Props3D/se14r-blaster/models/SE-14r_ScopeMount_V4.stl

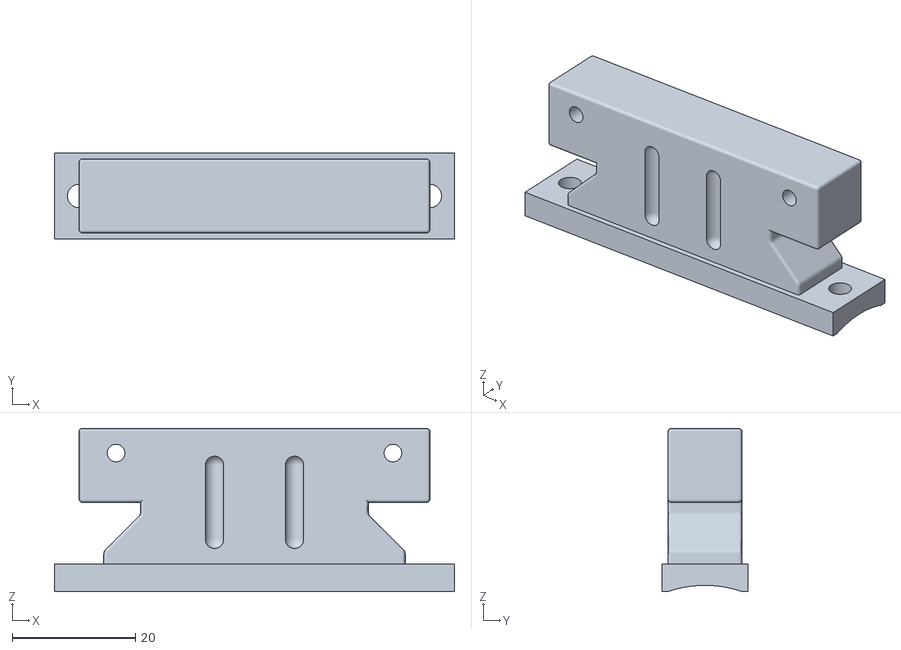
[picture p15: CAD file, 2021-10-15]
models/SE-14r_ScopeMount_V4.stl
65.0 x 14.0 x 26.5
