Props3D/se14r-blaster/models/SE-14r_UpperBack_V4.stl

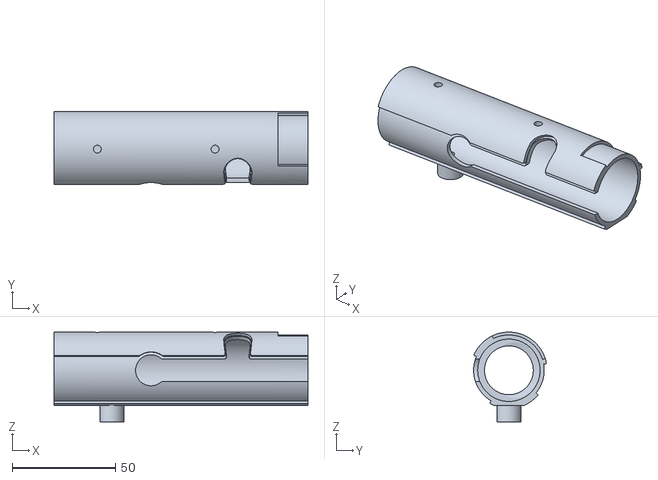
[picture p16: CAD file, 2021-10-15]
models/SE-14r_UpperBack_V4.stl
123.0 x 35.3 x 43.5
