Props3D/se14r-blaster/models/SE-14r_UpperFront_V4.stl

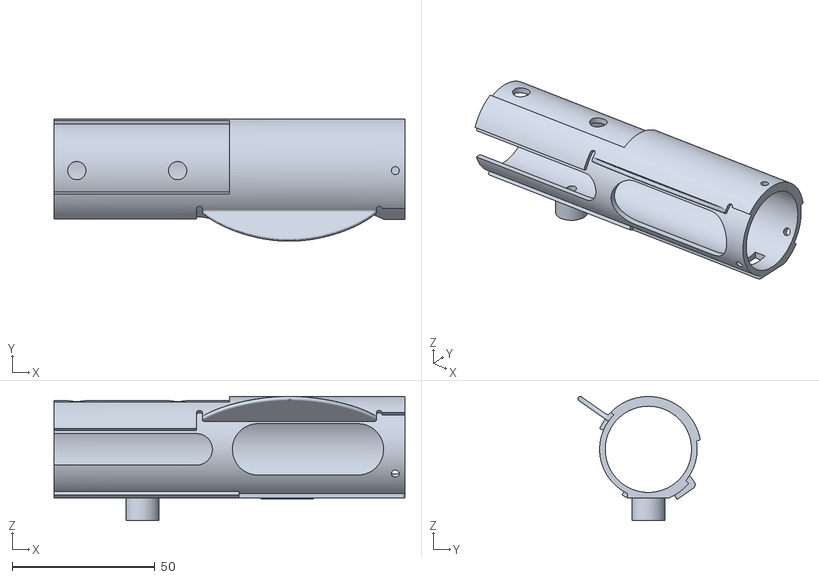
[picture p17: CAD file, 2021-10-15]
models/SE-14r_UpperFront_V4.stl
123.0 x 42.9 x 43.6
