Props3D/se14r-blaster/models/SE-14r_StockBracket_V4.stl

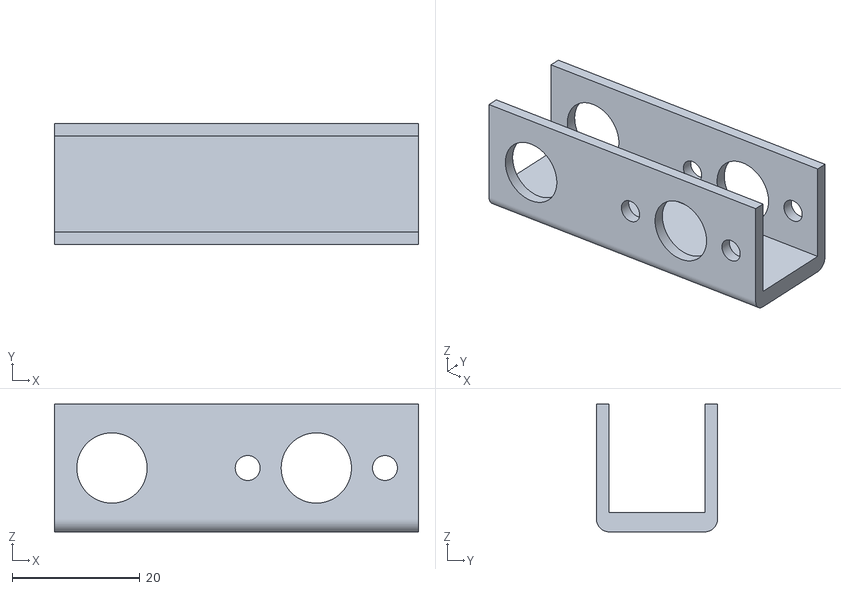
[picture p18: CAD file, 2021-10-15]
models/SE-14r_StockBracket_V4.stl
57.0 x 19.0 x 20.0
