Props3D/se14r-blaster/models/SE-14r_SightBottom_V4.stl

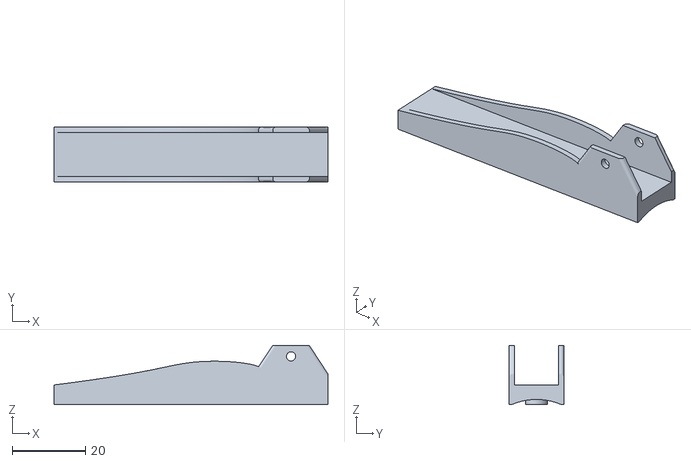
[picture p19: CAD file, 2021-10-15]
models/SE-14r_SightBottom_V4.stl
75.0 x 15.0 x 16.2
