Props3D/se14r-blaster/models/SE-14r_SwitchHolder_V4.stl

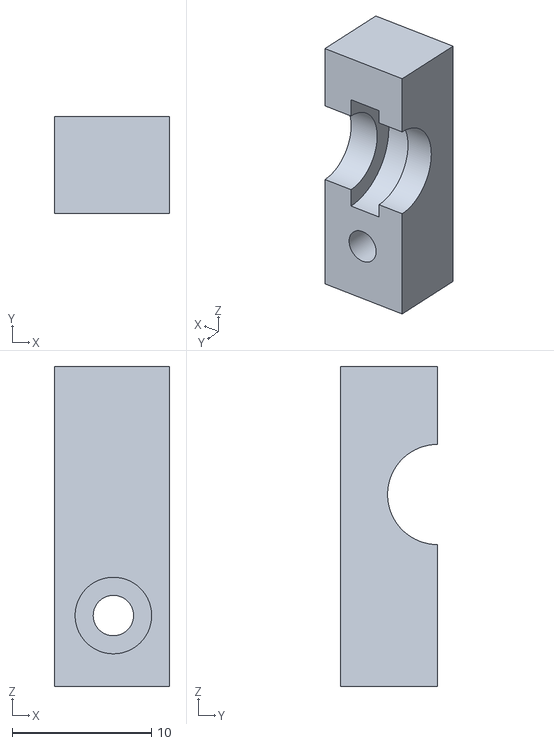
[picture p20: CAD file, 2021-10-15]
models/SE-14r_SwitchHolder_V4.stl
8.30 x 7.00 x 23.0
