Props3D/se14r-blaster/models/SE-14r_Selector_V4.stl

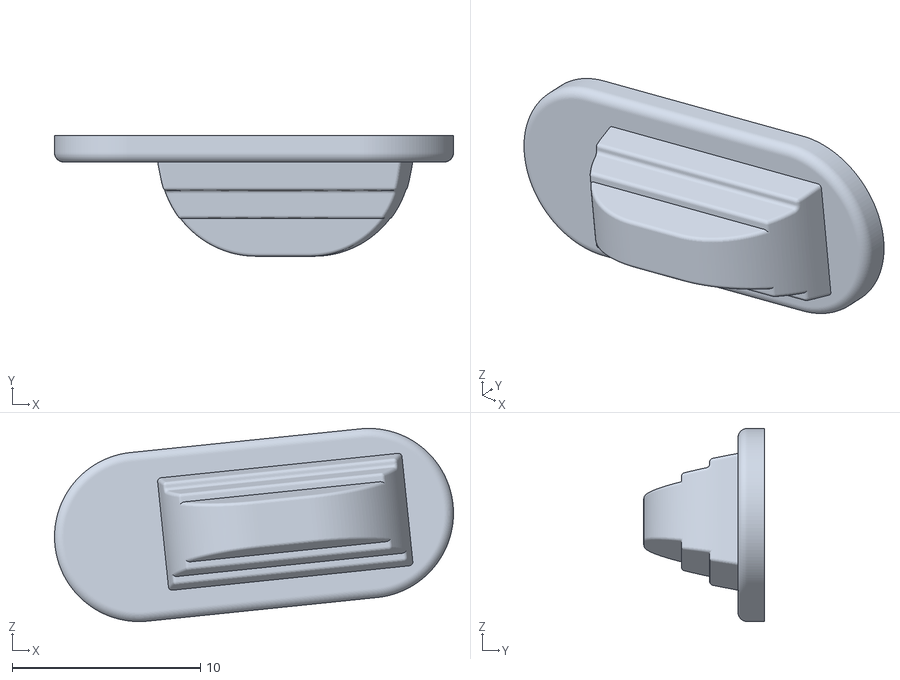
[picture p21: CAD file, 2021-10-15]
models/SE-14r_Selector_V4.stl
21.2 x 6.40 x 10.3
