Props3D/se14r-blaster/models/SE-14r_SightTop_V4.stl

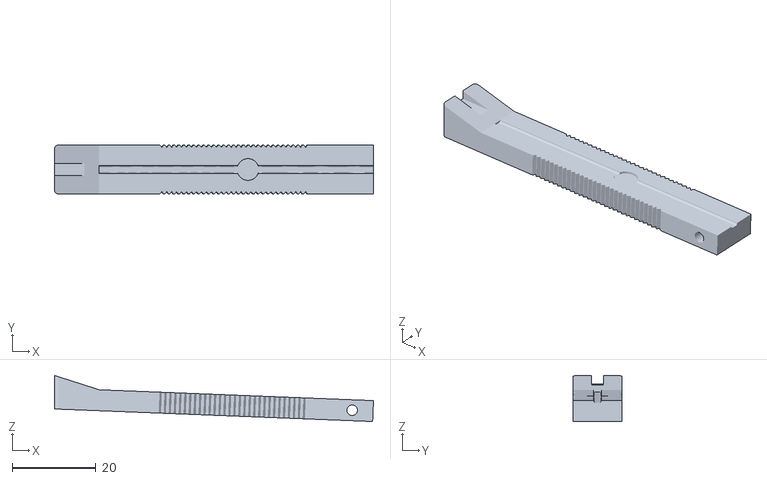
[picture p22: CAD file, 2021-10-15]
models/SE-14r_SightTop_V4.stl
76.2 x 11.8 x 11.0
